Montecri/GNSSTimeServer/images/IMG01.jpg

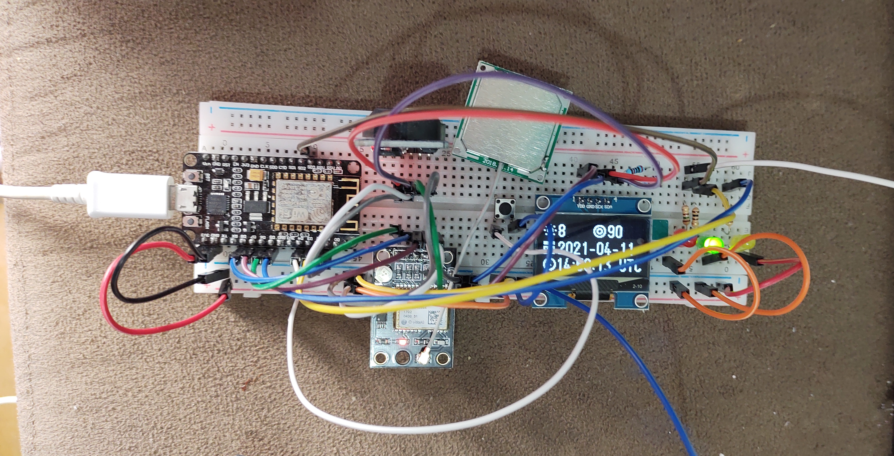
images/IMG01.jpg
