Montecri/GNSSTimeServer/images/IMG02.jpg

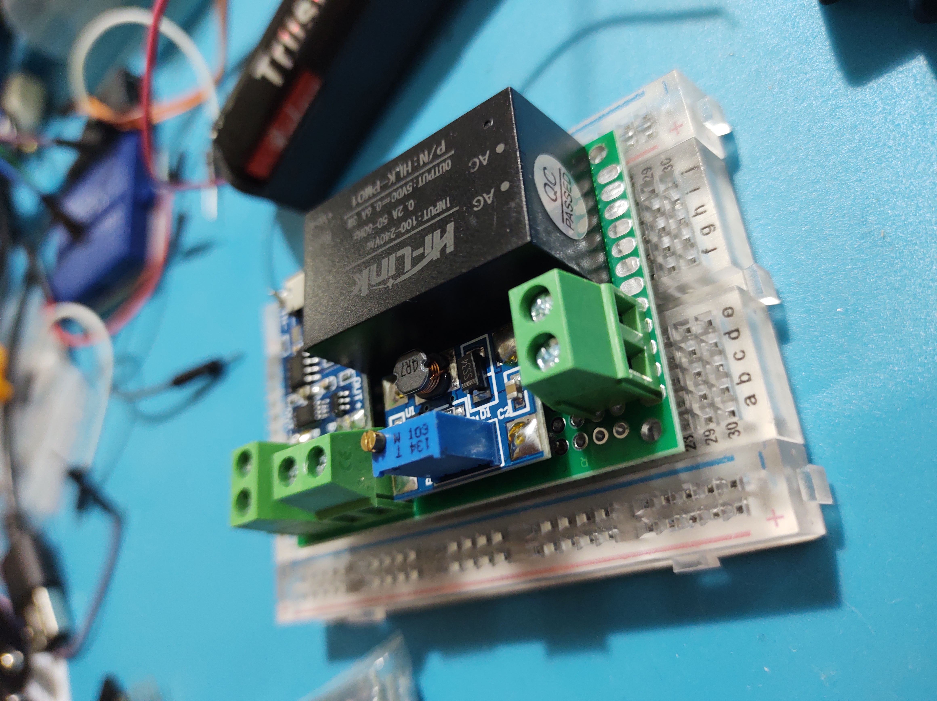
images/IMG02.jpg
