Montecri/GNSSTimeServer/images/IMG03.jpg

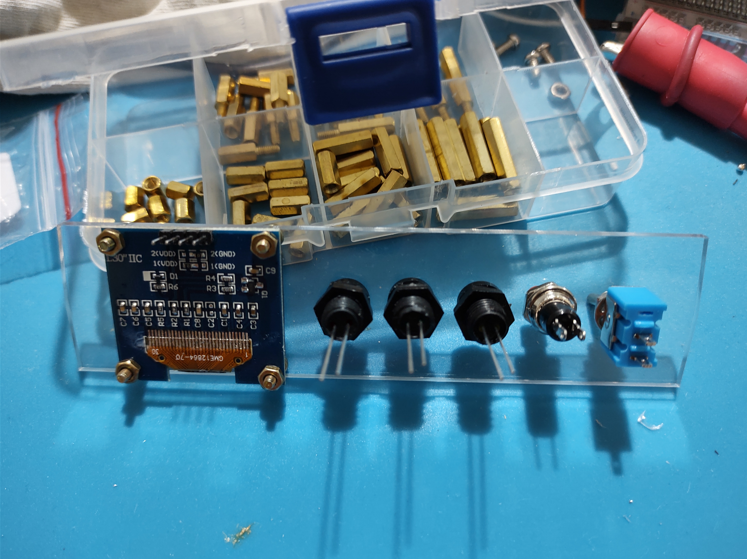
images/IMG03.jpg
