Montecri/GNSSTimeServer/images/IMG04.jpg

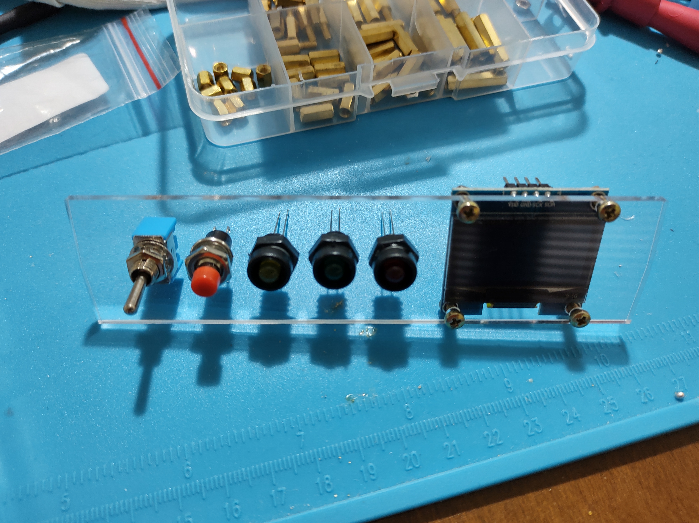
images/IMG04.jpg
