Montecri/GNSSTimeServer/images/IMG05.jpg

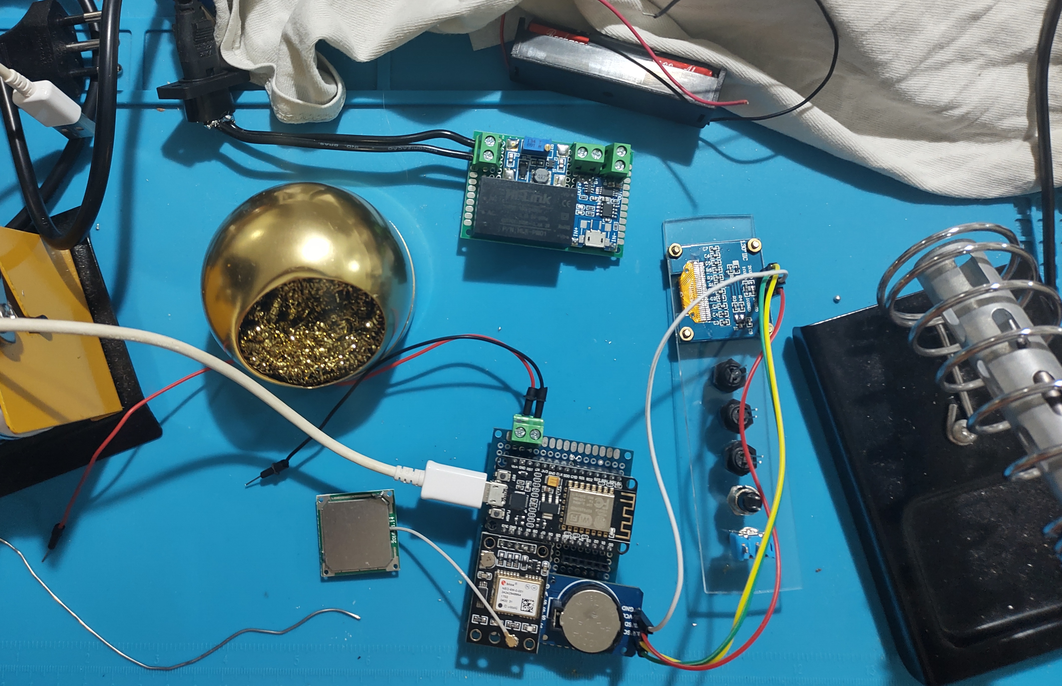
images/IMG05.jpg
