Montecri/GNSSTimeServer/images/IMG08.jpg

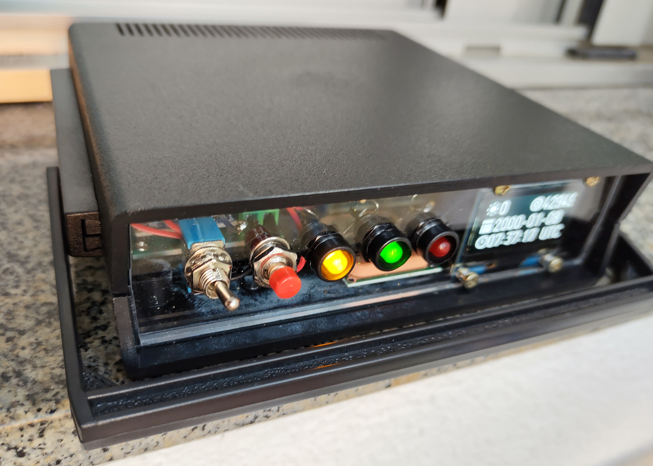
images/IMG08.jpg
