Montecri/GNSSTimeServer/images/IMG09.jpg

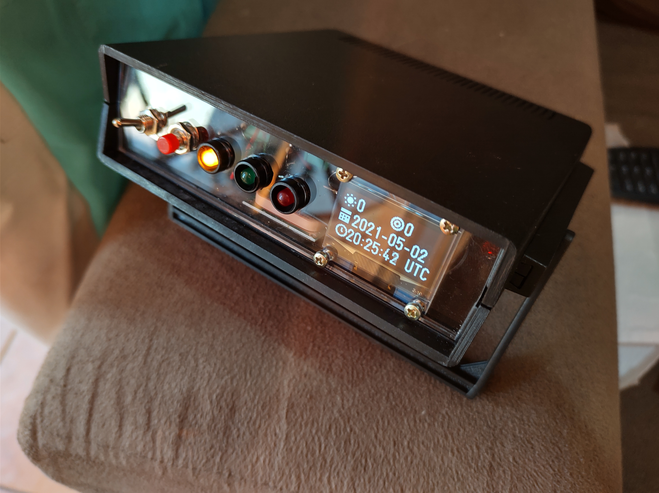
images/IMG09.jpg
