Montecri/GNSSTimeServer/images/IMG10.jpg

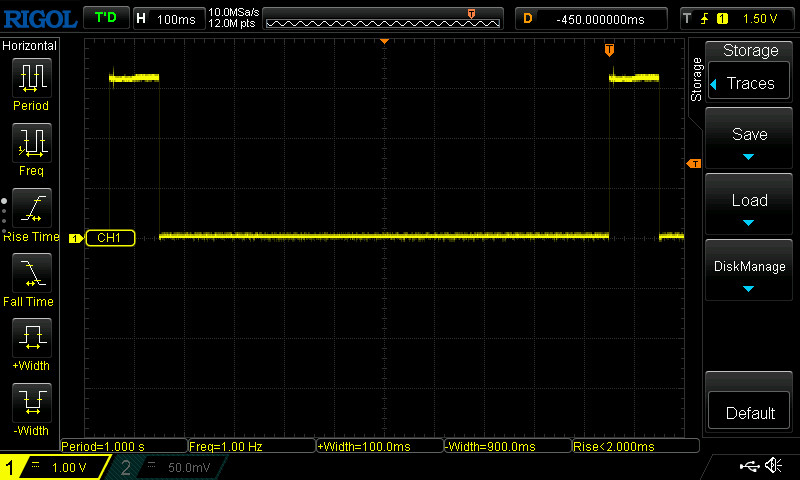
images/IMG10.jpg
