Montecri/GNSSTimeServer/images/IMG11.jpg

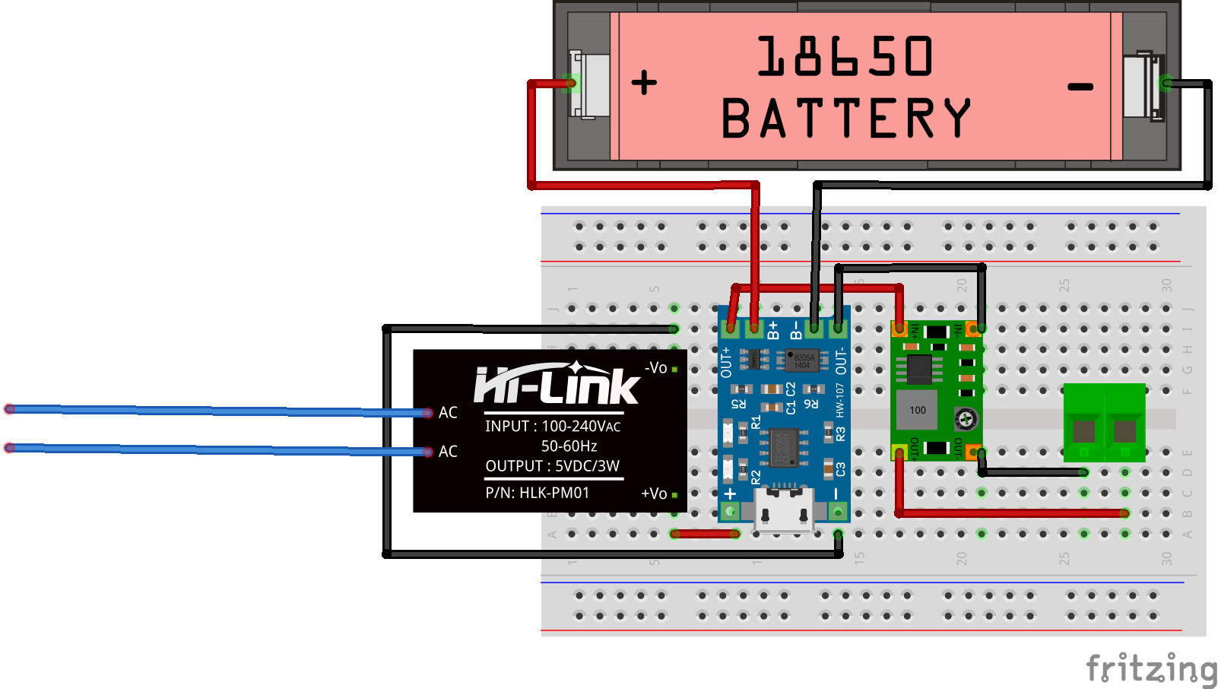
images/IMG11.jpg
