Montecri/GNSSTimeServer/images/IMG12.jpg

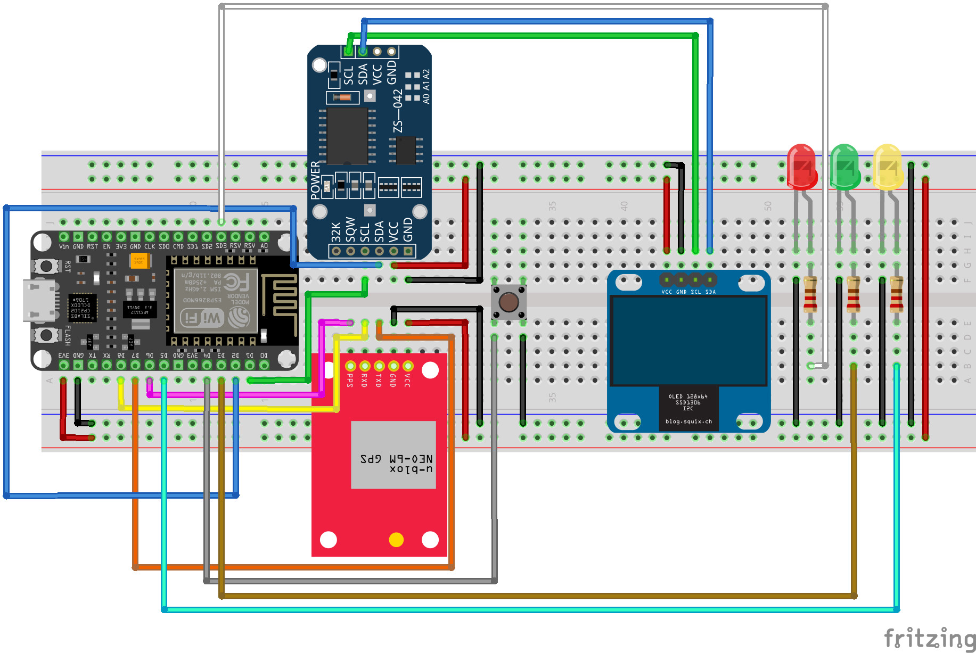
images/IMG12.jpg
