Montecri/GNSSTimeServer/images/sketch-ESP32_Without_ETH-20250308_bb.png

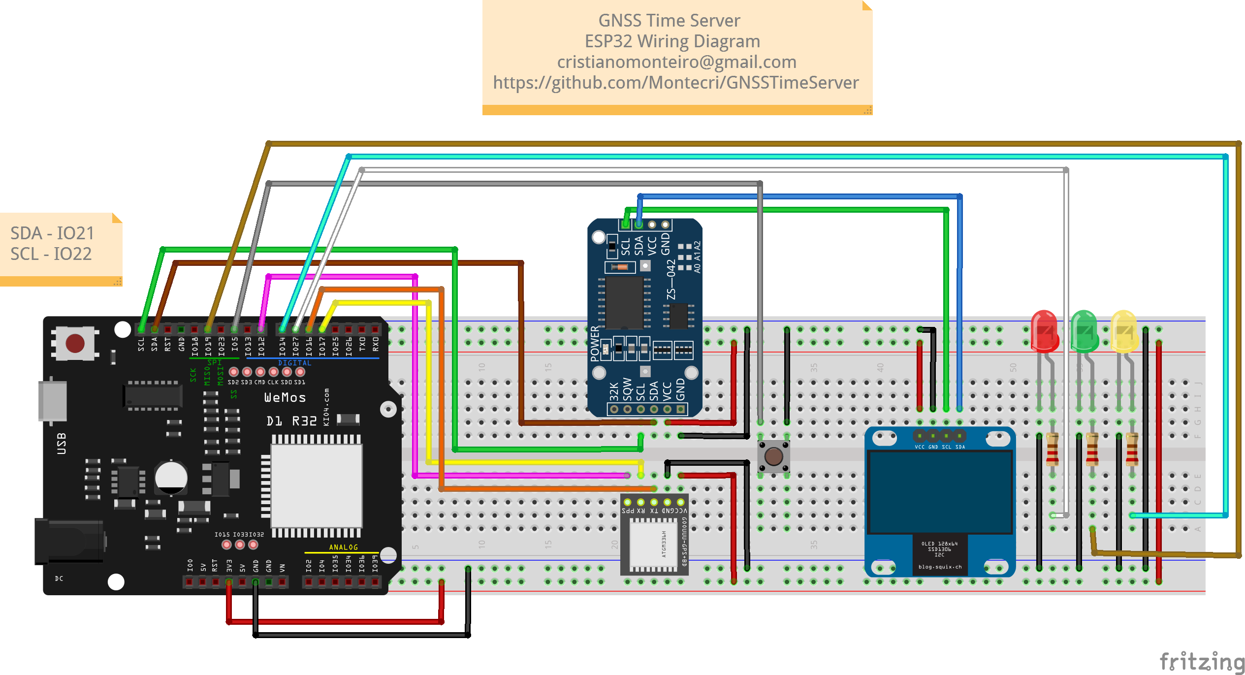
images/sketch-ESP32_Without_ETH-20250308_bb.png
