Montecri/GNSSTimeServer/src/NTP_RDATE/src/index_bytearray.h

#define index_gz_len 19559
const uint8_t index_gz[] PROGMEM = {
0x1F, 0x8B, 0x08, 0x08, 0x3B, 0x75, 0xDE, 0x64, 0x02, 0xFF, 0x69, 0x6E, 0x64, 0x65, 0x78, 0x2E, 0x68, 0x00, 0xEC, 0xBC, 0xD9, 0xCE, 0xF5, 0x48, 0x96, 0x1D, 0x76, 0x6D, 0x01, 0x7A, 0x87, 0xDF, 0x09, 0xF8, 0x8A, 0x2A, 0x71, 0x9E, 0xAA, 0x32, 0x0B, 0xE0, 0x4C, 0x1E, 0xCE, 0x33, 0x0F, 0x6F, 0x04, 0xCE, 0xF3, 0x3C, 0x1D, 0xF2, 0xE9, 0x7D, 0xFE, 0xCC, 0xEA, 0xB6, 0xBA, 0x5A, 0x36, 0xDA, 0x2E, 0xB5, 0x20, 0x03, 0xE2, 0xCD, 0x61, 0x04, 0xC9, 0x1D, 0x11, 0x3B, 0x22, 0xD6, 0x5E, 0x6B, 0x93, 0xDF, 0xF7, 0x6B, 0xBD, 0x0F, 0xFD, 0x5F, 0xFF, 0xE3, 0x7F, 0xF8, 0xF5, 0x7F, 0xE7, 0x4D, 0xCE, 0x7B, 0x5B, 0xC2, 0x8F, 0xBF, 0x55, 0xFC, 0xF8, 0xF1, 0x6B, 0x5D, 0x24, 0xF9, 0xEF, 0x67, 0xDF, 0xF3, 0xA1, 0xD8, 0x93, 0xEF, 0xA5, 0x7D, 0xFE, 0x53, 0xB1, 0x1C, 0xCD, 0xF9, 0xDB, 0x2F, 0xD9, 0x34, 0xEE, 0xC5, 0xB8, 0xFF, 0x69, 0xBF, 0xE7, 0xE2, 0x97, 0x1F, 0x7F, 0x2B, 0xFD, 0xF6, 0xCB, 0x5E, 0x7C, 0x76, 0xF0, 0xA7, 0x89, 0xBF, 0xFC, 0xC8, 0xEA, 0x64, 0xDD, 0x8A, 0xFD, 0x37, 0xDF, 0x13, 0xFF, 0x44, 0xFD, 0xF2, 0x2F, 0x0C, 0x8D, 0xC9, 0x50, 0xFC, 0xF6, 0xCB, 0xD9, 0x14, 0xD7, 0x3C, 0xAD, 0xFB, 0x7F, 0xF5, 0xF8, 0xD5, 0xE4, 0x7B, 0xFD, 0x5B, 0x5E, 0x9C, 0x4D, 0x56, 0xFC, 0xE9, 0xF7, 0xC2, 0x7F, 0xFA, 0xD1, 0x8C, 0xCD, 0xDE, 0x24, 0xFD, 0x9F, 0xB6, 0x2C, 0xE9, 0x8B, 0xDF, 0xE0, 0x7F, 0xB6, 0xB4, 0x37, 0x7B, 0x5F, 0xFC, 0x55, 0x70, 0xAD, 0x3F, 0x79, 0xCD, 0x50, 0xFC, 0xC9, 0x2D, 0xD6, 0xB3, 0x58, 0x7F, 0x05, 0xFF, 0xA8, 0xFE, 0x8F, 0xFF, 0xE1, 0x7F, 0xFB, 0xB5, 0x6F, 0xC6, 0xEE, 0xC7, 0x5A, 0xF4, 0xBF, 0xFD, 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
0x53, 0x4E, 0xCD, 0x96, 0xF1, 0x0C, 0x12, 0xA4, 0x58, 0xDE, 0x3A, 0xD1, 0x53, 0xE8, 0x91, 0xCD, 0x59, 0x26, 0xE1, 0x2E, 0x3F, 0x94, 0x1A, 0x3A, 0x4A, 0x56, 0x22, 0x34,
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
